thweasel/FujiSim_Test1/KiCad7/Z80Bus_Adapters/ZXspectrum_Concept/ZXspectrum_Concept.kicad_pcb

## KiCad design KiCad7/Z80Bus_Adapters/ZXspectrum_Concept/ZXspectrum_Concept.kicad_pcb (2023-06-03, an earlier design)

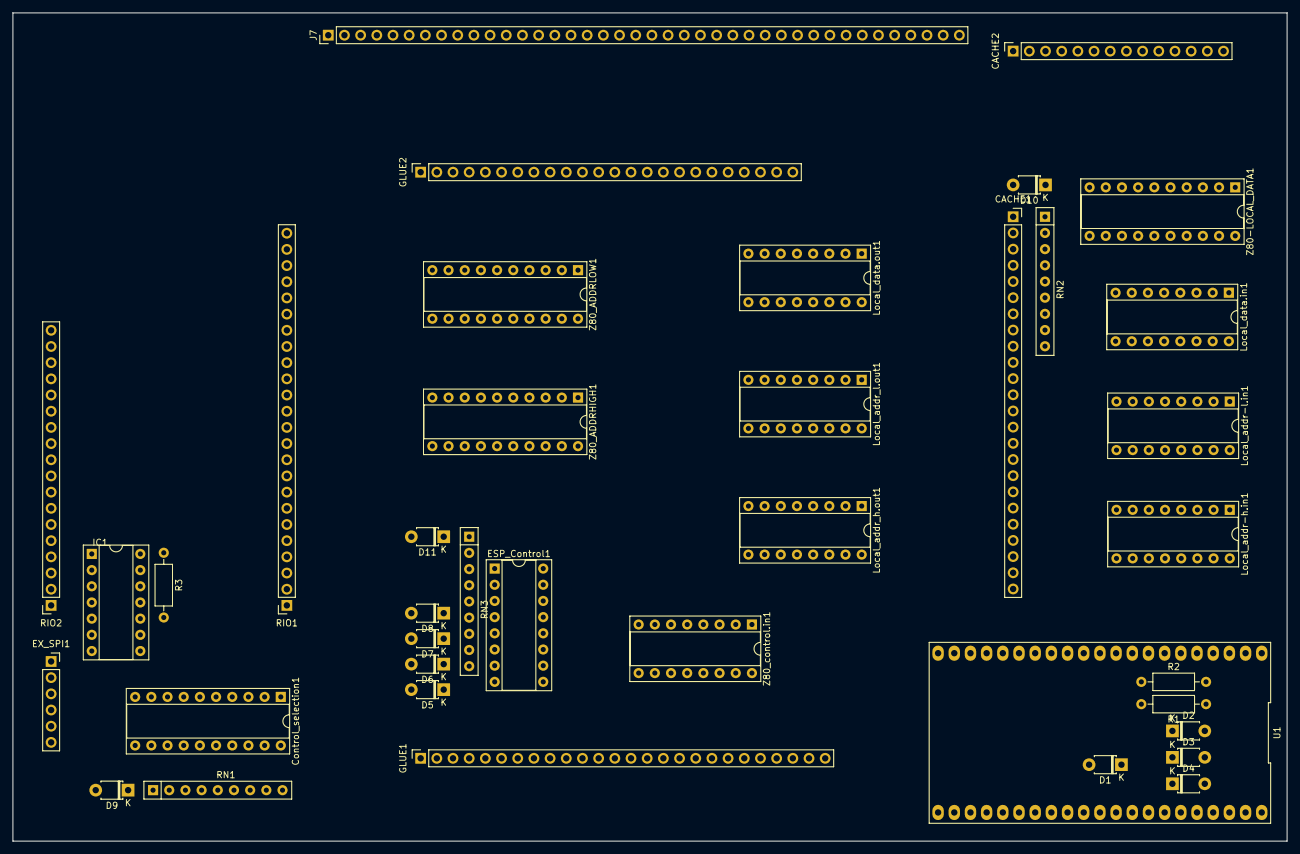
[picture p12: board ZXspectrum_Concept.kicad_pcb from above]

Board: 2 copper layers, 200.0 x 130.0 mm, 39 parts (0 on the bottom side), 130 nets, no tracks yet.

Parts:
CACHE1: Conn_01x24_Socket; PinSocket_1x24_P2.54mm_Vertical
CACHE2: Conn_01x14_Socket; PinSocket_1x14_P2.54mm_Vertical
Control_selection1: 74HC244N; DIP-20_W7.62mm_Socket
D1, D2, D3, D4, D5, D6, D7, D8, D9, D10, D11: 1N4148; D_T-1_P5.08mm_Horizontal
ESP_Control1: 74595N; DIP-16_W7.62mm_Socket
EX_SPI1: PinSocket_2.54mm; PinSocket_1x06_P2.54mm_Vertical
GLUE1: Conn_01x26_Socket; PinSocket_1x26_P2.54mm_Vertical
GLUE2: Conn_01x24_Socket; PinSocket_1x24_P2.54mm_Vertical
IC1: 74HC32N; DIP-14_W7.62mm_Socket
J7: DIAG-HOST_SYSTEM_BUS; PinHeader_1x40_P2.54mm_Vertical
Local_addr-h.in1: 74HC165N; DIP-16_W7.62mm_Socket
Local_addr-l.in1: 74HC165N; DIP-16_W7.62mm_Socket
Local_addr_h.out1: 74595N; DIP-16_W7.62mm_Socket
Local_addr_l.out1: 74595N; DIP-16_W7.62mm_Socket
Local_data.in1: 74HC165N; DIP-16_W7.62mm_Socket
Local_data.out1: 74595N; DIP-16_W7.62mm_Socket
R1, R2, R3: 22K; R_Axial_DIN0207_L6.3mm_D2.5mm_P10.16mm_Horizontal
RIO1: Conn_01x24_Socket; PinSocket_1x24_P2.54mm_Vertical
RIO2: Conn_01x18_Socket; PinSocket_1x18_P2.54mm_Vertical
RN1: LOCAL_CONTROL_BIAS; R_Array_SIP9
RN2, RN3: 4609M-101-103LF; R_Array_SIP9
U1: FREENOVE_ESP32-WROVER-DEV
Z80-LOCAL_DATA1, Z80_ADDRHIGH1, Z80_ADDRLOW1: 74HC245N; DIP-20_W7.62mm_Socket
Z80_control.in1: 74HC165N; DIP-16_W7.62mm_Socket

Connections:
+5V: CACHE2.1, Control_selection1.20 (VCC), D9.2 (A), D10.2 (A), D11.2 (A), ESP_Control1.16 (VCC), EX_SPI1.5, GLUE1.1, IC1.14 (VCC), Local_addr-h.in1.16 (VCC), Local_addr-l.in1.16 (VCC), Local_addr_h.out1.16 (VCC), Local_addr_l.out1.16 (VCC), Local_data.in1.16 (VCC), Local_data.out1.16 (VCC), R1.2, R3.1, RIO2.1, U1.20 (+5V), Z80-LOCAL_DATA1.20 (VCC), Z80_ADDRHIGH1.20 (VCC), Z80_ADDRLOW1.20 (VCC), Z80_control.in1.16 (VCC)
/CACHE connector/CACHE_CONTROL.A16: CACHE2.2, GLUE2.14
/CACHE connector/CACHE_CONTROL.CS: CACHE2.5, GLUE2.17
/CACHE connector/CACHE_CONTROL.DATASTATUS+PERM_Z80_IORQ: CACHE2.6, GLUE2.13
/CACHE connector/CACHE_CONTROL.OE: CACHE2.4, GLUE2.16
/CACHE connector/CACHE_CONTROL.WE: CACHE2.3, GLUE2.15
/CACHE connector/CACHE_DATASTATUS: CACHE2.12, GLUE2.5, RIO2.13
/CACHE connector/CACHE_SEL_0: CACHE2.8, RIO2.9
/CACHE connector/CACHE_SEL_1: CACHE2.9, RIO2.10
/CACHE connector/CACHE_SEL_2: CACHE2.10, RIO2.11
/CACHE connector/CACHE_SEL_3: CACHE2.11, RIO2.12
/CACHE connector/LOCAL_A0: CACHE1.9, Local_addr-l.in1.11 (D0), Local_addr_l.out1.15 (QA), Z80_ADDRLOW1.18 (B0)
/CACHE connector/LOCAL_A1: CACHE1.10, Local_addr-l.in1.12 (D1), Local_addr_l.out1.1 (QB), Z80_ADDRLOW1.17 (B1)
/CACHE connector/LOCAL_A2: CACHE1.11, Local_addr-l.in1.13 (D2), Local_addr_l.out1.2 (QC), Z80_ADDRLOW1.16 (B2)
/CACHE connector/LOCAL_A3: CACHE1.12, Local_addr-l.in1.14 (D3), Local_addr_l.out1.3 (QD), Z80_ADDRLOW1.15 (B3)
/CACHE connector/LOCAL_A4: CACHE1.13, Local_addr-l.in1.3 (D4), Local_addr_l.out1.4 (QE), Z80_ADDRLOW1.14 (B4)
/CACHE connector/LOCAL_A5: CACHE1.14, Local_addr-l.in1.4 (D5), Local_addr_l.out1.5 (QF), Z80_ADDRLOW1.13 (B5)
/CACHE connector/LOCAL_A6: CACHE1.15, Local_addr-l.in1.5 (D6), Local_addr_l.out1.6 (QG), Z80_ADDRLOW1.12 (B6)
/CACHE connector/LOCAL_A7: CACHE1.16, Local_addr-l.in1.6 (D7), Local_addr_l.out1.7 (QH), Z80_ADDRLOW1.11 (B7)
/CACHE connector/LOCAL_A8: CACHE1.17, Local_addr-h.in1.11 (D0), Local_addr_h.out1.15 (QA), Z80_ADDRHIGH1.18 (B0)
/CACHE connector/LOCAL_A9: CACHE1.18, Local_addr-h.in1.12 (D1), Local_addr_h.out1.1 (QB), Z80_ADDRHIGH1.17 (B1)
/CACHE connector/LOCAL_A10: CACHE1.19, Local_addr-h.in1.13 (D2), Local_addr_h.out1.2 (QC), Z80_ADDRHIGH1.16 (B2)
/CACHE connector/LOCAL_A11: CACHE1.20, Local_addr-h.in1.14 (D3), Local_addr_h.out1.3 (QD), Z80_ADDRHIGH1.15 (B3)
/CACHE connector/LOCAL_A12: CACHE1.21, Local_addr-h.in1.3 (D4), Local_addr_h.out1.4 (QE), Z80_ADDRHIGH1.14 (B4)
/CACHE connector/LOCAL_A13: CACHE1.22, Local_addr-h.in1.4 (D5), Local_addr_h.out1.5 (QF), Z80_ADDRHIGH1.13 (B5)
/CACHE connector/LOCAL_A14: CACHE1.23, Local_addr-h.in1.5 (D6), Local_addr_h.out1.6 (QG), Z80_ADDRHIGH1.12 (B6)
/CACHE connector/LOCAL_A15: CACHE1.24, Local_addr-h.in1.6 (D7), Local_addr_h.out1.7 (QH), Z80_ADDRHIGH1.11 (B7)
/CACHE connector/LOCAL_D0: CACHE1.1, Local_data.in1.11 (D0), Local_data.out1.15 (QA), RN2.2 (R1), Z80-LOCAL_DATA1.18 (B0)
/CACHE connector/LOCAL_D1: CACHE1.2, Local_data.in1.12 (D1), Local_data.out1.1 (QB), RN2.3 (R2), Z80-LOCAL_DATA1.17 (B1)
/CACHE connector/LOCAL_D2: CACHE1.3, Local_data.in1.13 (D2), Local_data.out1.2 (QC), RN2.4 (R3), Z80-LOCAL_DATA1.16 (B2)
/CACHE connector/LOCAL_D3: CACHE1.4, Local_data.in1.14 (D3), Local_data.out1.3 (QD), RN2.5 (R4), Z80-LOCAL_DATA1.15 (B3)
/CACHE connector/LOCAL_D4: CACHE1.5, Local_data.in1.3 (D4), Local_data.out1.4 (QE), RN2.6 (R5), Z80-LOCAL_DATA1.14 (B4)
/CACHE connector/LOCAL_D5: CACHE1.6, Local_data.in1.4 (D5), Local_data.out1.5 (QF), RN2.7 (R6), Z80-LOCAL_DATA1.13 (B5)
/CACHE connector/LOCAL_D6: CACHE1.7, Local_data.in1.5 (D6), Local_data.out1.6 (QG), RN2.8 (R7), Z80-LOCAL_DATA1.12 (B6)
/CACHE connector/LOCAL_D7: CACHE1.8, Local_data.in1.6 (D7), Local_data.out1.7 (QH), RN2.9 (R8), Z80-LOCAL_DATA1.11 (B7)
/CACHE connector/Z80_HARDLOCK: CACHE2.7, GLUE1.22, U1.4 (GPIO39)
/CORE/ESP_HARDLOCK: GLUE1.20, U1.26 (GPIO2)
/CORE/ESP_INT: D2.2 (A), D3.2 (A), D4.2 (A), R1.1, R2.2, U1.3 (GPIO36)
/CORE/ESP_PULSE: IC1.1, U1.11 (GPIO27)
/CORE/ESP_ROMSEL_0: GLUE1.18, U1.23 (GPIO7)
/CORE/ESP_ROMSEL_1: GLUE1.19, U1.22 (GPIO6)
/CORE/ESP_ROM_WR_PROTECT: GLUE1.17, U1.28 (GPIO4)
/CORE/ESP_SPI_INT.CE: Local_addr-h.in1.15 (~CE), Local_addr-l.in1.15 (~CE), Local_data.in1.15 (~CE), U1.31 (GPIO5), Z80_control.in1.15 (~CE)
/CORE/ESP_SPI_INT.MISO: Local_addr-h.in1.7 (~Q7), U1.33 (GPIO19)
/CORE/ESP_SPI_INT.MOSI: Local_data.out1.14 (SER), U1.39 (GPIO23)
/CORE/ESP_SPI_INT.MR: ESP_Control1.10 (~SRCLR), Local_addr_h.out1.10 (~SRCLR), Local_addr_l.out1.10 (~SRCLR), Local_data.out1.10 (~SRCLR), R3.2
/CORE/ESP_SPI_INT.OE: ESP_Control1.13 (~OE), Local_addr_h.out1.13 (~OE), Local_addr_l.out1.13 (~OE), U1.8 (GPIO33)
/CORE/ESP_SPI_INT.PL: Local_addr-h.in1.1 (~PL), Local_addr-l.in1.1 (~PL), Local_data.in1.1 (~PL), U1.9 (GPIO25), Z80_control.in1.1 (~PL)
/CORE/ESP_SPI_INT.SCK: ESP_Control1.11 (SRCLK), Local_addr-h.in1.2 (CP), Local_addr-l.in1.2 (CP), Local_addr_h.out1.11 (SRCLK), Local_addr_l.out1.11 (SRCLK), Local_data.in1.2 (CP), Local_data.out1.11 (SRCLK), U1.32 (GPIO18), Z80_control.in1.2 (CP)
/CORE/ESP_SPI_INT.STC: ESP_Control1.12 (RCLK), Local_addr_h.out1.12 (RCLK), Local_addr_l.out1.12 (RCLK), Local_data.out1.12 (RCLK), U1.10 (GPIO26)
/CORE/ESP_WAIT_RESET: GLUE2.6, U1.18 (GPIO11)
/CORE/EX_MISO: EX_SPI1.3, U1.13 (GPIO12)
/CORE/EX_MOSI: EX_SPI1.4, U1.15 (GPIO13)
/CORE/EX_SCK: EX_SPI1.2, U1.12 (GPIO14)
/CORE/EX_SS: EX_SPI1.1, U1.25 (GPIO8)
/CORE/SD_CARD_SS: U1.24 (GPIO15), U1.38 (GPIO22)
/CORE/Z80_HARDLOCK_RESET: D3.1 (K), GLUE2.3, RIO2.15
/GLUE connector/!ESP_HARDLOCK: Control_selection1.19 (2OE), GLUE1.21
/GLUE connector/PERM_Z80_IORQ: GLUE1.24, RIO2.17
/GLUE connector/RIO_CONTROL.A14: GLUE2.20, RIO2.4
/GLUE connector/RIO_CONTROL.A15: GLUE2.19, RIO2.3
/GLUE connector/RIO_CONTROL.A16: GLUE2.18, RIO2.2
/GLUE connector/RIO_CONTROL.CE: GLUE2.23, RIO2.6
/GLUE connector/RIO_CONTROL.OE: GLUE2.22, RIO2.7
/GLUE connector/RIO_CONTROL.ROM_RDY: GLUE2.24, RIO2.8
/GLUE connector/RIO_CONTROL.WE: GLUE2.21, RIO2.5
/GLUE connector/WAIT_IO: GLUE2.4, RIO2.14
/GLUE connector/Z80_BUS_CONTROL.Z80_ADD_DIR: GLUE2.10, Z80_ADDRHIGH1.1 (A->B), Z80_ADDRLOW1.1 (A->B)
/GLUE connector/Z80_BUS_CONTROL.Z80_ADD_OE: GLUE2.9, Z80_ADDRHIGH1.19 (CE), Z80_ADDRLOW1.19 (CE)
/GLUE connector/Z80_BUS_CONTROL.Z80_DATA_DIR: GLUE2.11, Z80-LOCAL_DATA1.1 (A->B)
/GLUE connector/Z80_BUS_CONTROL.Z80_DATA_OE: GLUE2.12, Z80-LOCAL_DATA1.19 (CE)
/GLUE connector/Z80_HARDLOCK_SET: GLUE2.2, RIO2.16
/RIO connector/Z80_A0: GLUE2.1, J7.18, RIO1.9, Z80_ADDRLOW1.2 (A0)
/RIO connector/Z80_A1: J7.17, RIO1.10, Z80_ADDRLOW1.3 (A1)
/RIO connector/Z80_A2: J7.16, RIO1.11, Z80_ADDRLOW1.4 (A2)
/RIO connector/Z80_A3: J7.15, RIO1.12, Z80_ADDRLOW1.5 (A3)
/RIO connector/Z80_A4: J7.14, RIO1.13, Z80_ADDRLOW1.6 (A4)
/RIO connector/Z80_A5: J7.13, RIO1.14, Z80_ADDRLOW1.7 (A5)
/RIO connector/Z80_A6: J7.12, RIO1.15, Z80_ADDRLOW1.8 (A6)
/RIO connector/Z80_A7: J7.11, RIO1.16, Z80_ADDRLOW1.9 (A7)
/RIO connector/Z80_A8: J7.26, RIO1.17, Z80_ADDRHIGH1.2 (A0)
/RIO connector/Z80_A9: J7.25, RIO1.18, Z80_ADDRHIGH1.3 (A1)
/RIO connector/Z80_A10: J7.24, RIO1.19, Z80_ADDRHIGH1.4 (A2)
/RIO connector/Z80_A11: J7.23, RIO1.20, Z80_ADDRHIGH1.5 (A3)
/RIO connector/Z80_A12: J7.22, RIO1.21, Z80_ADDRHIGH1.6 (A4)
/RIO connector/Z80_A13: J7.21, RIO1.22, Z80_ADDRHIGH1.7 (A5)
/RIO connector/Z80_A14: GLUE2.7, J7.20, RIO1.23, Z80_ADDRHIGH1.8 (A6)
/RIO connector/Z80_A15: GLUE2.8, J7.19, RIO1.24, Z80_ADDRHIGH1.9 (A7)
/RIO connector/Z80_D0: J7.34, RIO1.1, Z80-LOCAL_DATA1.2 (A0)
/RIO connector/Z80_D1: J7.33, RIO1.2, Z80-LOCAL_DATA1.3 (A1)
/RIO connector/Z80_D2: J7.32, RIO1.3, Z80-LOCAL_DATA1.4 (A2)
/RIO connector/Z80_D3: J7.31, RIO1.4, Z80-LOCAL_DATA1.5 (A3)
/RIO connector/Z80_D4: J7.30, RIO1.5, Z80-LOCAL_DATA1.6 (A4)
/RIO connector/Z80_D5: J7.29, RIO1.6, Z80-LOCAL_DATA1.7 (A5)
/RIO connector/Z80_D6: J7.28, RIO1.7, Z80-LOCAL_DATA1.8 (A6)
/RIO connector/Z80_D7: J7.27, RIO1.8, Z80-LOCAL_DATA1.9 (A7)
/SPI/ESP_CONTROL.BUSRQ: Control_selection1.1 (1OE), D8.1 (K), ESP_Control1.4 (QE), GLUE1.15, RN3.6 (R5)
/SPI/ESP_CONTROL.IORQ: Control_selection1.6 (1A2), Control_selection1.13 (2A2), ESP_Control1.2 (QC), GLUE1.13, RN3.4 (R3)
/SPI/ESP_CONTROL.MEMRQ: Control_selection1.8 (1A3), Control_selection1.11 (2A3), ESP_Control1.3 (QD), GLUE1.14, RN3.5 (R4)
/SPI/ESP_CONTROL.NMI: D5.1 (K), ESP_Control1.7 (QH), RN3.9 (R8)
/SPI/ESP_CONTROL.RD: Control_selection1.2 (1A0), Control_selection1.17 (2A0), ESP_Control1.15 (QA), RN3.2 (R1)
/SPI/ESP_CONTROL.ROMCS: D6.1 (K), ESP_Control1.6 (QG), GLUE1.16, RN3.8 (R7)
/SPI/ESP_CONTROL.WAIT: D7.1 (K), ESP_Control1.5 (QF), RN3.7 (R6)
/SPI/ESP_CONTROL.WR: ESP_Control1.1 (QB), GLUE1.12, IC1.2, Local_data.out1.13 (~OE), RN3.3 (R2)
/SPI/ESP_CONTROL.WR+ESP_PULSE: Control_selection1.4 (1A1), Control_selection1.15 (2A1), IC1.3
/SPI/LOCAL_CONTROL.IORQ: Control_selection1.14 (1Y2), GLUE1.10, RN1.3 (R2)
/SPI/LOCAL_CONTROL.MEMRQ: Control_selection1.12 (1Y3), GLUE1.11, RN1.2 (R1)
/SPI/LOCAL_CONTROL.RD: Control_selection1.18 (1Y0), GLUE1.8, RN1.5 (R4)
/SPI/LOCAL_CONTROL.WR: Control_selection1.16 (1Y1), GLUE1.9, RN1.4 (R3)
/SPI/Z80_CONTROL.BUSACK: D4.1 (K), J7.9, Z80_control.in1.5 (D6)
/SPI/Z80_CONTROL.BUSRQ: D8.2 (A), GLUE1.6, J7.5, Z80_control.in1.3 (D4)
/SPI/Z80_CONTROL.IORQ: Control_selection1.7 (2Y2), GLUE1.4, J7.3, Z80_control.in1.13 (D2)
/SPI/Z80_CONTROL.MEMRQ: Control_selection1.9 (2Y3), GLUE1.5, J7.4, Z80_control.in1.14 (D3)
/SPI/Z80_CONTROL.NMI: D5.2 (A), J7.7, Z80_control.in1.6 (D7)
/SPI/Z80_CONTROL.RD: Control_selection1.3 (2Y0), GLUE1.2, J7.1, Z80_control.in1.11 (D0)
/SPI/Z80_CONTROL.RESET: D1.2 (A), J7.10
/SPI/Z80_CONTROL.ROMCS: D6.2 (A), J7.8
/SPI/Z80_CONTROL.WAIT: D2.1 (K), D7.2 (A), GLUE1.7, J7.6, Z80_control.in1.4 (D5)
/SPI/Z80_CONTROL.WR: Control_selection1.5 (2Y1), GLUE1.3, J7.2, Z80_control.in1.12 (D1)
GND: CACHE2.14, Control_selection1.10 (GND), ESP_Control1.8 (GND), EX_SPI1.6, GLUE1.26, IC1.4, IC1.5, IC1.7 (GND), IC1.9, IC1.10, IC1.12, IC1.13, J7.40, Local_addr-h.in1.8 (GND), Local_addr-l.in1.8 (GND), Local_addr_h.out1.8 (GND), Local_addr_l.out1.8 (GND), Local_data.in1.8 (GND), Local_data.in1.10 (DS), Local_data.out1.8 (GND), R2.1, RIO2.18, U1.21 (GND), U1.34 (GND), U1.40 (GND), Z80-LOCAL_DATA1.10 (GND), Z80_ADDRHIGH1.10 (GND), Z80_ADDRLOW1.10 (GND), Z80_control.in1.8 (GND)
unnamed: D1.1 (K), U1.35 (GPIO21)
unnamed: D9.1 (K), RN1.1 (common)
unnamed: D10.1 (K), RN2.1 (common)
unnamed: D11.1 (K), RN3.1 (common)
unnamed: ESP_Control1.9 (QH'), Local_addr_l.out1.14 (SER)
unnamed: ESP_Control1.14 (SER), Local_data.out1.9 (QH')
unnamed: Local_addr-h.in1.10 (DS), Local_addr-l.in1.7 (~Q7)
unnamed: Local_addr-l.in1.10 (DS), Z80_control.in1.7 (~Q7)
unnamed: Local_addr_h.out1.14 (SER), Local_addr_l.out1.9 (QH')
unnamed: Local_data.in1.7 (~Q7), Z80_control.in1.10 (DS)
