thweasel/FujiSim_Test1/KiCad7/Z80Bus_ReferenceDesign/FujiNet_FinishedPCBs/FujiNet_Z80Bus_Reference_singleboard.kicad_pcb

## KiCad design KiCad7/Z80Bus_ReferenceDesign/FujiNet_FinishedPCBs/FujiNet_Z80Bus_Reference_singleboard.kicad_pcb (2023-05-09)

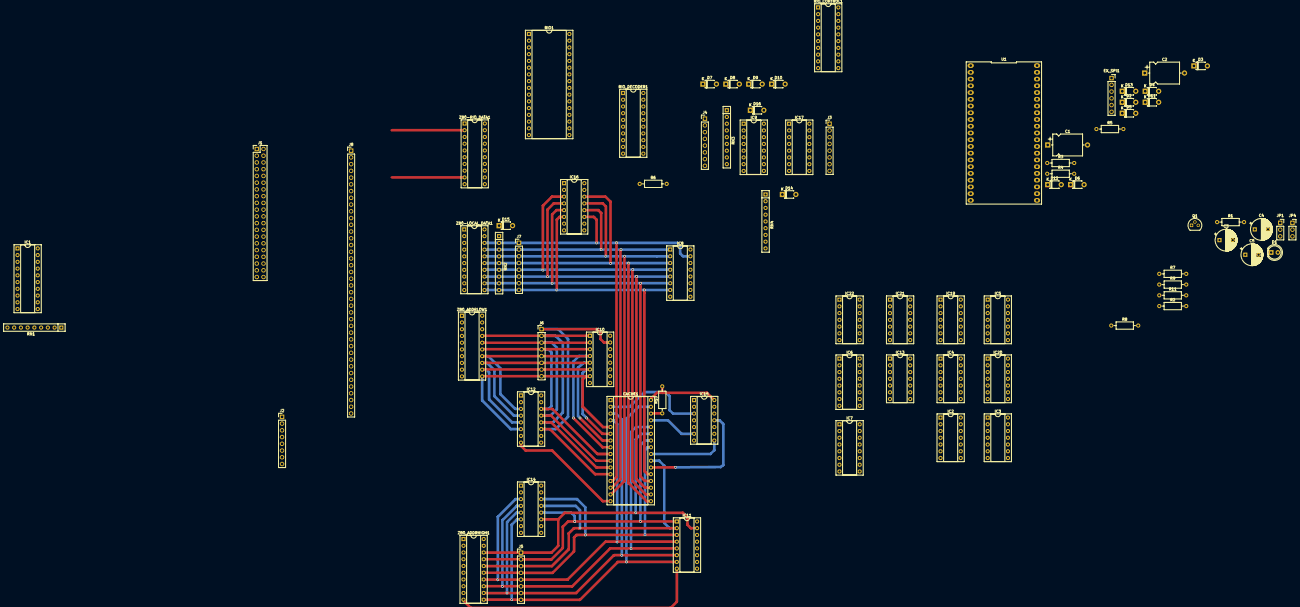
[picture p13: board FujiNet_Z80Bus_Reference_singleboard.kicad_pcb from above]

Board: 2 copper layers, 78 parts (0 on the bottom side), 165 nets.

Parts:
C1, C2: 10UF; CP_Axial_L11.0mm_D8.0mm_P15.00mm_Horizontal
C3: 10 uf; CP_Radial_D8.0mm_P5.00mm
C4, C5: .1 uf; CP_Radial_D8.0mm_P5.00mm
CACHE1: AS6C1008-55PCN; DIP-32_W15.24mm_Socket
D1: POWER_LED; LED_D5.0mm
D2, D3, D4, D5, D6, D7, D8, D9, D10, D11, D12, D13, D14, D15, D16: 1N4148; D_T-1_P5.08mm_Horizontal
EX_SPI1: PINHD-1X6; PinSocket_1x06_P2.54mm_Vertical
IC1: 74244N; DIP-20_W7.62mm_Socket
IC2: 7404N; DIP-14_W7.62mm_Socket
IC3: 7474N; DIP-14_W7.62mm_Socket
IC4, IC13, IC19, IC21, IC22: 7432N; DIP-14_W7.62mm_Socket
IC5, IC15, IC20: 7408N; DIP-14_W7.62mm_Socket
IC6, IC7: 74590N; DIP-16_W7.62mm_Socket
IC8, IC9, IC10, IC11: 74595N; DIP-16_W7.62mm_Socket
IC12, IC14, IC16, IC17: 74165N; DIP-16_W7.62mm_Socket
J1: HOST SYSTEM HEADER; PinHeader_2x20_P2.54mm_Vertical
J2: DIAG-ESP_SPI; PinHeader_1x08_P2.54mm_Vertical
J3: DIAG-Z80_CONTROL; PinHeader_1x08_P2.54mm_Vertical
J4: DIAG-ESP_CONTROL; PinHeader_1x08_P2.54mm_Vertical
J5: DIAG-LOCAL_ADD_HIGH; PinHeader_1x08_P2.54mm_Vertical
J6: DIAG-LOCAL_ADD_LOW; PinHeader_1x08_P2.54mm_Vertical
J7: DIAG-LOCAL_DATA; PinHeader_1x08_P2.54mm_Vertical
J8: DIAG-HOST_SYSTEM_BUS; PinHeader_1x40_P2.54mm_Vertical
JP1: PINHD-ADDR_FILTER; PinSocket_1x03_P2.54mm_Vertical
JP4: PINHD-POWER/RESET; PinSocket_1x03_P2.54mm_Vertical
Q1: 2N2222 (BC337); TO-92
R1, R2, R7: 1K; R_Axial_DIN0207_L6.3mm_D2.5mm_P10.16mm_Horizontal
R3, R4, R5, R6: 22K; R_Axial_DIN0207_L6.3mm_D2.5mm_P10.16mm_Horizontal
R8, R9, R10, R11: 10K; R_Axial_DIN0207_L6.3mm_D2.5mm_P10.16mm_Horizontal
RIO1: AS6C1008-55PCN; DIP-32_W15.24mm_Socket
RIO_CONTROL1: 74244N; DIP-20_W7.62mm_Socket
RIO_DECODER1: 74245N; DIP-20_W7.62mm_Socket
RN1, RN2, RN3, RN4: 4609M-101-103LF; R_Array_SIP9
U1: FREENOVE_ESP32-WROVER-DEV
Z80-LOCAL_DATA1, Z80-RIO_DATA1, Z80_ADDRHIGH1, Z80_ADDRLOW1: 74245N; DIP-20_W7.62mm_Socket

Connections:
/!CACHE_DATASTATUS: IC21.2, Q1.1, R7.1
/CACHE/CACHE_CE2: CACHE1.30, R10.1
/CACHE/CACHE_CS: CACHE1.22, IC15.11
/CACHE/CACHE_DATASTATUS+PERM_Z80_IORQ: IC6.11, IC6.13, IC13.6
/CACHE/CACHE_OE: CACHE1.24, IC15.8
/CACHE/CACHE_WE: CACHE1.29, IC15.6
/CACHE/LOCAL_ADD_0: CACHE1.12, IC6.15, IC10.15, IC12.11, J6.1, Z80_ADDRLOW1.18
/CACHE/LOCAL_ADD_1: CACHE1.11, IC6.1, IC10.1, IC12.12, J6.2, Z80_ADDRLOW1.17
/CACHE/LOCAL_ADD_2: CACHE1.10, IC6.2, IC10.2, IC12.13, J6.3, Z80_ADDRLOW1.16
/CACHE/LOCAL_ADD_3: CACHE1.9, IC6.3, IC10.3, IC12.14, J6.4, Z80_ADDRLOW1.15
/CACHE/LOCAL_ADD_4: CACHE1.8, IC6.4, IC10.4, IC12.3, J6.5, Z80_ADDRLOW1.14
/CACHE/LOCAL_ADD_5: CACHE1.7, IC6.5, IC10.5, IC12.4, J6.6, Z80_ADDRLOW1.13
/CACHE/LOCAL_ADD_6: CACHE1.6, IC6.6, IC10.6, IC12.5, J6.7, Z80_ADDRLOW1.12
/CACHE/LOCAL_ADD_7: CACHE1.5, IC6.7, IC10.7, IC12.6, J6.8, Z80_ADDRLOW1.11
/CACHE/LOCAL_ADD_8: CACHE1.27, IC7.15, IC11.15, IC14.11, J5.1, Z80_ADDRHIGH1.18
/CACHE/LOCAL_ADD_9: CACHE1.26, IC7.1, IC11.1, IC14.12, J5.2, Z80_ADDRHIGH1.17
/CACHE/LOCAL_ADD_10: CACHE1.23, IC7.2, IC11.2, IC14.13, J5.3, Z80_ADDRHIGH1.16
/CACHE/LOCAL_ADD_11: CACHE1.25, IC7.3, IC11.3, IC14.14, J5.4, Z80_ADDRHIGH1.15
/CACHE/LOCAL_ADD_12: CACHE1.4, IC11.4, IC14.3, J5.5, Z80_ADDRHIGH1.14
/CACHE/LOCAL_DATA_0: CACHE1.13, IC8.15, IC16.11, J7.1, RN2.2, Z80-LOCAL_DATA1.18
/CACHE/LOCAL_DATA_1: CACHE1.14, IC8.1, IC16.12, J7.2, RN2.3, Z80-LOCAL_DATA1.17
/CACHE/LOCAL_DATA_2: CACHE1.15, IC8.2, IC16.13, J7.3, RN2.4, Z80-LOCAL_DATA1.16
/CACHE/LOCAL_DATA_3: CACHE1.17, IC8.3, IC16.14, J7.4, RN2.5, Z80-LOCAL_DATA1.15
/CACHE/LOCAL_DATA_4: CACHE1.18, IC8.4, IC16.3, J7.5, RN2.6, Z80-LOCAL_DATA1.14
/CACHE/LOCAL_DATA_5: CACHE1.19, IC8.5, IC16.4, J7.6, RN2.7, Z80-LOCAL_DATA1.13
/CACHE/LOCAL_DATA_6: CACHE1.20, IC8.6, IC16.5, J7.7, RN2.8, Z80-LOCAL_DATA1.12
/CACHE/LOCAL_DATA_7: CACHE1.21, IC8.7, IC16.6, J7.8, RN2.9, Z80-LOCAL_DATA1.11
/CACHE_DATASTATUS: IC6.12, IC6.14, IC7.12, IC7.14, IC13.5, IC15.1, R2.1, R9.1, RIO_DECODER1.14
/CACHE_SEL_0: CACHE1.28, IC11.5, IC14.4, J5.6, RIO_DECODER1.18, Z80_ADDRHIGH1.13
/CACHE_SEL_1: CACHE1.3, IC11.6, IC14.5, J5.7, RIO_DECODER1.17, Z80_ADDRHIGH1.12
/CACHE_SEL_2: CACHE1.31, IC11.7, IC14.6, J5.8, RIO_DECODER1.16, Z80_ADDRHIGH1.11
/CACHE_SEL_3: CACHE1.2, IC15.3, RIO_DECODER1.15
/CORE/!ESP_HARDLOCK: IC1.1, IC2.2
/CORE/CLR_Z80_HARDLOCK: IC3.1, IC5.3
/CORE/ESP_CONTROL_Z80: D2.1, D3.1, IC1.19
/CORE/ESP_HARDLOCK: IC2.1, IC13.2, IC13.9, U1.26
/CORE/ESP_INT: D6.2, D11.2, D12.2, R3.2, R5.2, U1.3
/CORE/ESP_PULSE: IC13.12, U1.11
/CORE/ESP_SPI.CE: IC12.15, IC14.15, IC16.15, IC17.15, J2.7, U1.31
/CORE/ESP_SPI.MISO: IC14.9, J2.2, U1.33
/CORE/ESP_SPI.MOSI: IC8.14, J2.1, U1.39
/CORE/ESP_SPI.OE: IC9.13, IC10.13, IC11.13, J2.5, U1.8
/CORE/ESP_SPI.PL: IC12.1, IC14.1, IC16.1, IC17.1, J2.8, U1.9
/CORE/ESP_SPI.SCK: IC8.11, IC9.11, IC10.11, IC11.11, IC12.2, IC14.2, IC16.2, IC17.2, J2.6, U1.32
/CORE/ESP_SPI.STC: IC8.12, IC9.12, IC10.12, IC11.12, J2.3, U1.10
/CORE/ESP_WAIT_RESET: C1.1, IC3.13, RN1.8, U1.18
/CORE/EX_MISO: EX_SPI1.3, U1.13
/CORE/EX_MOSI: EX_SPI1.4, U1.15
/CORE/EX_SCK: EX_SPI1.2, U1.12
/CORE/EX_SS: EX_SPI1.1, U1.25
/CORE/IORQ_FILTER_BIT: IC21.12, JP1.2
/CORE/PRE_Z80_HARDLOCK: IC3.4, IC13.3
/CORE/SD_CARD_SS: U1.24, U1.38
/CORE/SPIBUS/ESP_SPI.MR: IC8.10, IC9.10, IC10.10, IC11.10, R6.2
/CORE/Z80_ADD_CONNECT: D2.2, IC22.1, RN1.6
/CORE/Z80_DATA_CONNECT: D3.2, IC21.10, IC22.12, RN1.7
/ESP_CONTROL_BUSRQ: D7.1, IC4.10, IC9.4, J4.5, RN3.6
/ESP_CONTROL_IORQ: IC1.8, IC1.17, IC5.5, IC9.3, J4.4, RN3.4
/ESP_CONTROL_MEMRQ: IC1.6, IC1.15, IC5.4, IC9.2, IC22.5, J4.3, RN3.5
/ESP_CONTROL_NMI: D10.1, IC9.7, J4.8, RN3.9
/ESP_CONTROL_RD: IC1.2, IC1.11, IC9.15, J4.1, RN3.2
/ESP_CONTROL_ROMCS: D9.1, IC9.6, IC19.9, J4.7, RN3.8
/ESP_CONTROL_WAIT: D8.1, IC9.5, J4.6, RN3.7
/ESP_CONTROL_WR: IC8.13, IC9.1, IC13.13, IC21.9, J2.4, J4.2, RN3.3
/ESP_IOD_CONFIG: IC4.8, IC19.1, IC19.5, IC20.5, IC20.12, IC22.4
/ESP_ROMSEL_0: RIO_CONTROL1.11, U1.23
/ESP_ROMSEL_1: RIO_CONTROL1.13, U1.22
/LOCAL_IORQ: IC1.14, IC15.2, RN1.5
/LOCAL_MEMRQ: IC1.12, IC15.13, RN1.4
/LOCAL_RD: IC1.18, IC15.10, RN1.2
/LOCAL_WR: IC1.16, IC15.5, RN1.3
/PERM_Z80_IORQ: IC13.4, IC15.12, IC20.1, IC20.4, IC21.1, IC21.5, IC21.11, IC22.13, RIO_DECODER1.19
/RIO/DEC14: RIO1.3, RIO_CONTROL1.9, RIO_CONTROL1.18, RN4.2
/RIO/DEC15: RIO1.31, RIO_CONTROL1.7, RIO_CONTROL1.16, RN4.3
/RIO/DEC16: IC20.6, IC20.10, RIO1.2, RIO_CONTROL1.1
/RIO/DEC_CE: IC20.8, RIO1.22
/RIO/DEC_OE: RIO1.24, RIO_CONTROL1.3, RIO_CONTROL1.12, RN4.5, Z80-RIO_DATA1.1
/RIO/DEC_WE: RIO1.29, RIO_CONTROL1.5, RIO_CONTROL1.14, RN4.4
/RIO/ESP_IOD_CONFIG+Z80_WR: IC19.3, RIO_CONTROL1.6
/RIO/RIO_CE2: R11.1, RIO1.30
/RIO/ROM_D0: RIO1.13, RIO_DECODER1.2, Z80-RIO_DATA1.18
/RIO/ROM_D1: RIO1.14, RIO_DECODER1.3, Z80-RIO_DATA1.17
/RIO/ROM_D2: RIO1.15, RIO_DECODER1.4, Z80-RIO_DATA1.16
/RIO/ROM_D3: RIO1.17, RIO_DECODER1.5, Z80-RIO_DATA1.15
/RIO/ROM_D4: RIO1.18, RIO_DECODER1.6, Z80-RIO_DATA1.14
/RIO/ROM_D5: RIO1.19, RIO_DECODER1.7, Z80-RIO_DATA1.13
/RIO/ROM_D6: RIO1.20, RIO_DECODER1.8, Z80-RIO_DATA1.12
/RIO/ROM_D7: RIO1.21, RIO_DECODER1.9, Z80-RIO_DATA1.11
/RIO/ROM_D_RDY: IC19.8, IC20.13, RIO_CONTROL1.19, Z80-RIO_DATA1.19
/RIO/ROM_WR_PROTECT+Z80_WR: IC19.11, RIO_CONTROL1.15
/RIO/Z80_A0: J1.1, J8.20, RIO1.12, Z80_ADDRLOW1.2
/RIO/Z80_A1: J1.2, J8.21, RIO1.11, Z80_ADDRLOW1.3
/RIO/Z80_A2: J1.3, J8.22, RIO1.10, Z80_ADDRLOW1.4
/RIO/Z80_A3: J1.4, J8.23, RIO1.9, Z80_ADDRLOW1.5
/RIO/Z80_A4: J1.5, J8.24, RIO1.8, Z80_ADDRLOW1.6
/RIO/Z80_A5: J1.6, J8.25, RIO1.7, Z80_ADDRLOW1.7
/RIO/Z80_A6: J1.7, J8.26, RIO1.6, Z80_ADDRLOW1.8
/RIO/Z80_A7: J1.8, J8.27, RIO1.5, Z80_ADDRLOW1.9
/RIO/Z80_A8: J1.33, J8.28, RIO1.27, Z80_ADDRHIGH1.2
/RIO/Z80_A9: J1.34, J8.29, RIO1.26, Z80_ADDRHIGH1.3
/RIO/Z80_A10: J1.35, J8.30, RIO1.23, Z80_ADDRHIGH1.4
/RIO/Z80_A11: J1.36, J8.31, RIO1.25, Z80_ADDRHIGH1.5
/RIO/Z80_A12: J1.37, J8.32, RIO1.4, Z80_ADDRHIGH1.6
/RIO/Z80_A13: J1.38, J8.33, RIO1.28, Z80_ADDRHIGH1.7
/RIO/Z80_A14: J1.39, J8.34, RIO_CONTROL1.2, Z80_ADDRHIGH1.8
/RIO/Z80_A15: J1.40, J8.35, RIO_CONTROL1.4, Z80_ADDRHIGH1.9
/RIO/Z80_D0: J1.9, J8.12, Z80-LOCAL_DATA1.2, Z80-RIO_DATA1.2
/RIO/Z80_D1: J1.10, J8.13, Z80-LOCAL_DATA1.3, Z80-RIO_DATA1.3
/RIO/Z80_D2: J1.11, J8.14, Z80-LOCAL_DATA1.4, Z80-RIO_DATA1.4
/RIO/Z80_D3: J1.12, J8.15, Z80-LOCAL_DATA1.5, Z80-RIO_DATA1.5
/RIO/Z80_D4: J1.13, J8.16, Z80-LOCAL_DATA1.6, Z80-RIO_DATA1.6
/RIO/Z80_D5: J1.14, J8.17, Z80-LOCAL_DATA1.7, Z80-RIO_DATA1.7
/RIO/Z80_D6: J1.15, J8.18, Z80-LOCAL_DATA1.8, Z80-RIO_DATA1.8
/RIO/Z80_D7: J1.16, J8.19, Z80-LOCAL_DATA1.9, Z80-RIO_DATA1.9
/RIO/Z80_RD+ESP_IOD_CONFIG+PERM_Z80_IORQ: IC20.3, RIO_CONTROL1.8
/ROM_WR_PROTECT: IC19.13, U1.28
/WAIT_IO: IC2.9, RIO_DECODER1.13
/Z80 BUS/Z80_ADD_DIR: IC22.6, Z80_ADDRHIGH1.1, Z80_ADDRLOW1.1
/Z80 BUS/Z80_ADD_OE: IC22.3, Z80_ADDRHIGH1.19, Z80_ADDRLOW1.19
/Z80 BUS/Z80_DATA_DIR: IC22.8, Z80-LOCAL_DATA1.1
/Z80 BUS/Z80_DATA_OE: IC22.11, Z80-LOCAL_DATA1.19
/Z80_BUSACK: IC17.6, J1.24, J3.8, J8.10
/Z80_BUSRQ: D7.2, IC17.3, J1.28, J3.5, J8.6
/Z80_HARDLOCK: IC3.5, IC6.10, IC7.10, U1.4
/Z80_HARDLOCK_RESET: D11.1, IC2.5, RIO_DECODER1.12
/Z80_HARDLOCK_SET: IC2.3, RIO_DECODER1.11
/Z80_IORQ: IC1.5, IC13.10, IC17.13, J1.29, J3.3, J8.5
/Z80_MEMRQ: IC1.3, IC17.14, IC19.10, J1.30, J3.4, J8.4
/Z80_NMI: D10.2, D12.1, IC17.5, J1.26, J3.7, J8.8
/Z80_RD: IC1.9, IC15.9, IC17.11, IC19.4, IC21.4, J1.32, J3.1, J8.2, RIO_CONTROL1.17
/Z80_RESET: D4.2, J1.23, J8.11, JP4.1
/Z80_ROMCS: D9.2, J1.25, J8.9
/Z80_WAIT: D6.1, D8.2, D13.2, IC17.4, J1.27, J3.6, J8.7
/Z80_WR: IC1.7, IC15.4, IC17.12, IC19.2, IC19.12, J1.31, J3.2, J8.3
GND: C1.2, C2.2, C3.2, C4.2, C5.2, CACHE1.16, D1.2, EX_SPI1.6, IC16.10, J1.21, J8.1, JP1.1, JP4.2, Q1.3, R5.1, RIO1.16, U1.14, U1.21, U1.34, U1.40
unnamed: C2.1, IC5.1, R4.2
unnamed: D1.1, R1.1
unnamed: D4.1, U1.35
unnamed: D5.1, RN1.1
unnamed: D13.1, IC3.8
unnamed: D14.1, RN4.1
unnamed: D15.1, RN2.1
unnamed: D16.1, RN3.1
unnamed: IC1.4, IC1.13, IC13.11
unnamed: IC2.6, IC5.2
unnamed: IC2.8, IC3.10
unnamed: IC2.10, IC4.9
unnamed: IC2.11, IC5.6
unnamed: IC6.9, IC7.11, IC7.13
unnamed: IC8.9, IC9.14
unnamed: IC10.9, IC11.14
unnamed: IC9.9, IC10.14
unnamed: IC12.9, IC14.10
unnamed: IC12.10, IC17.9
unnamed: IC2.4, IC13.1
unnamed: IC13.8, IC21.13
unnamed: IC16.9, IC17.10
unnamed: IC19.6, IC20.2
unnamed: IC20.9, IC20.11
unnamed: IC21.3, IC22.2
unnamed: IC21.6, IC22.9
unnamed: IC21.8, IC22.10
unnamed: Q1.2, R2.2
unnamed: R8.1, RIO_DECODER1.1
VCC: C3.1, C4.1, C5.1, CACHE1.32, D5.2, D14.2, D15.2, D16.2, EX_SPI1.5, J1.22, JP4.3, R1.2, R3.1, R4.1, R6.1, R7.2, R8.2, R9.2, R10.2, R11.2, RIO1.32, U1.19, U1.20
