thweasel/FujiSim_Test1/KiCad7/FujiNet_Z80Bus_Modules/RIO-128K_ZXspectrum/RIO-128K_ZXspectrum_connector.kicad_sch

## KiCad design KiCad7/FujiNet_Z80Bus_Modules/RIO-128K_ZXspectrum/RIO-128K_ZXspectrum_connector.kicad_sch (2023-06-01)

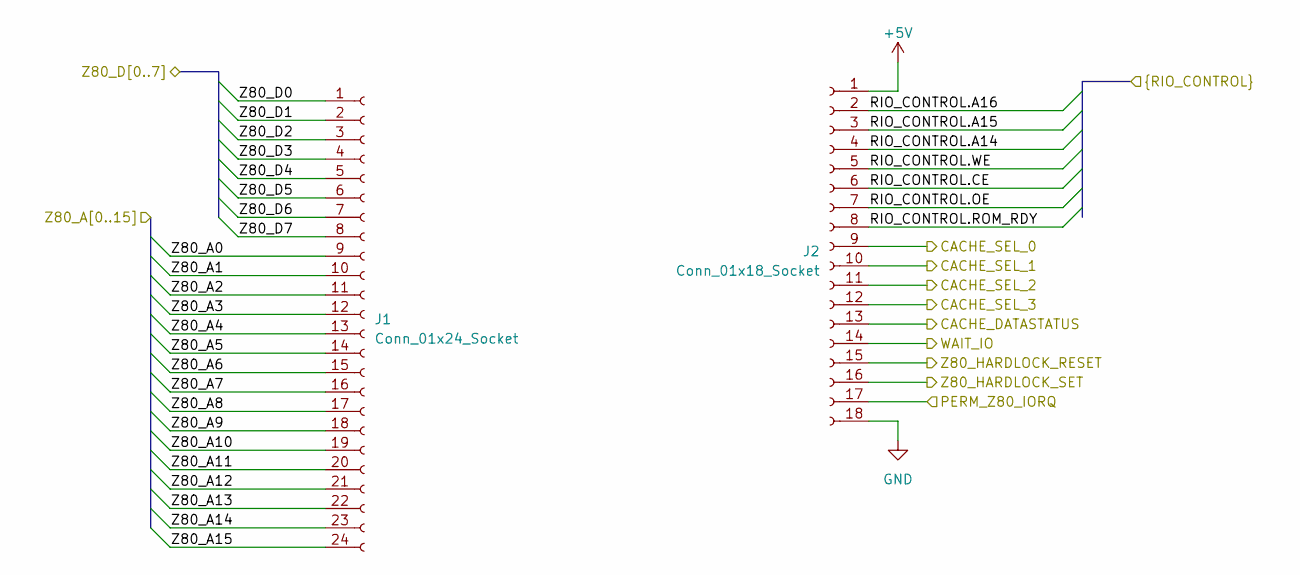
[picture p14: schematic RIO-128K_ZXspectrum_connector.kicad_sch]

Parts:
J1: Conn_01x24_Socket; PinSocket_1x24_P2.54mm_Vertical
J2: Conn_01x18_Socket; PinSocket_1x18_P2.54mm_Vertical

Connections:
+5V: J2.1
CACHE_DATASTATUS: J2.13
CACHE_SEL_0: J2.9
CACHE_SEL_1: J2.10
CACHE_SEL_2: J2.11
CACHE_SEL_3: J2.12
GND: J2.18
PERM_Z80_IORQ: J2.17
RIO_CONTROL.A14: J2.4
RIO_CONTROL.A15: J2.3
RIO_CONTROL.A16: J2.2
RIO_CONTROL.CE: J2.6
RIO_CONTROL.OE: J2.7
RIO_CONTROL.ROM_RDY: J2.8
RIO_CONTROL.WE: J2.5
WAIT_IO: J2.14
Z80_A0: J1.9
Z80_A1: J1.10
Z80_A2: J1.11
Z80_A3: J1.12
Z80_A4: J1.13
Z80_A5: J1.14
Z80_A6: J1.15
Z80_A7: J1.16
Z80_A8: J1.17
Z80_A9: J1.18
Z80_A10: J1.19
Z80_A11: J1.20
Z80_A12: J1.21
Z80_A13: J1.22
Z80_A14: J1.23
Z80_A15: J1.24
Z80_D0: J1.1
Z80_D1: J1.2
Z80_D2: J1.3
Z80_D3: J1.4
Z80_D4: J1.5
Z80_D5: J1.6
Z80_D6: J1.7
Z80_D7: J1.8
Z80_HARDLOCK_RESET: J2.15
Z80_HARDLOCK_SET: J2.16
