thweasel/FujiSim_Test1/KiCad7/FujiNet_Z80Bus_Modules/SPI-Z80-BUS_ZXspectrum/SPI-Z080-BUS_read.kicad_sch

## KiCad design KiCad7/FujiNet_Z80Bus_Modules/SPI-Z80-BUS_ZXspectrum/SPI-Z080-BUS_read.kicad_sch (2023-06-03)

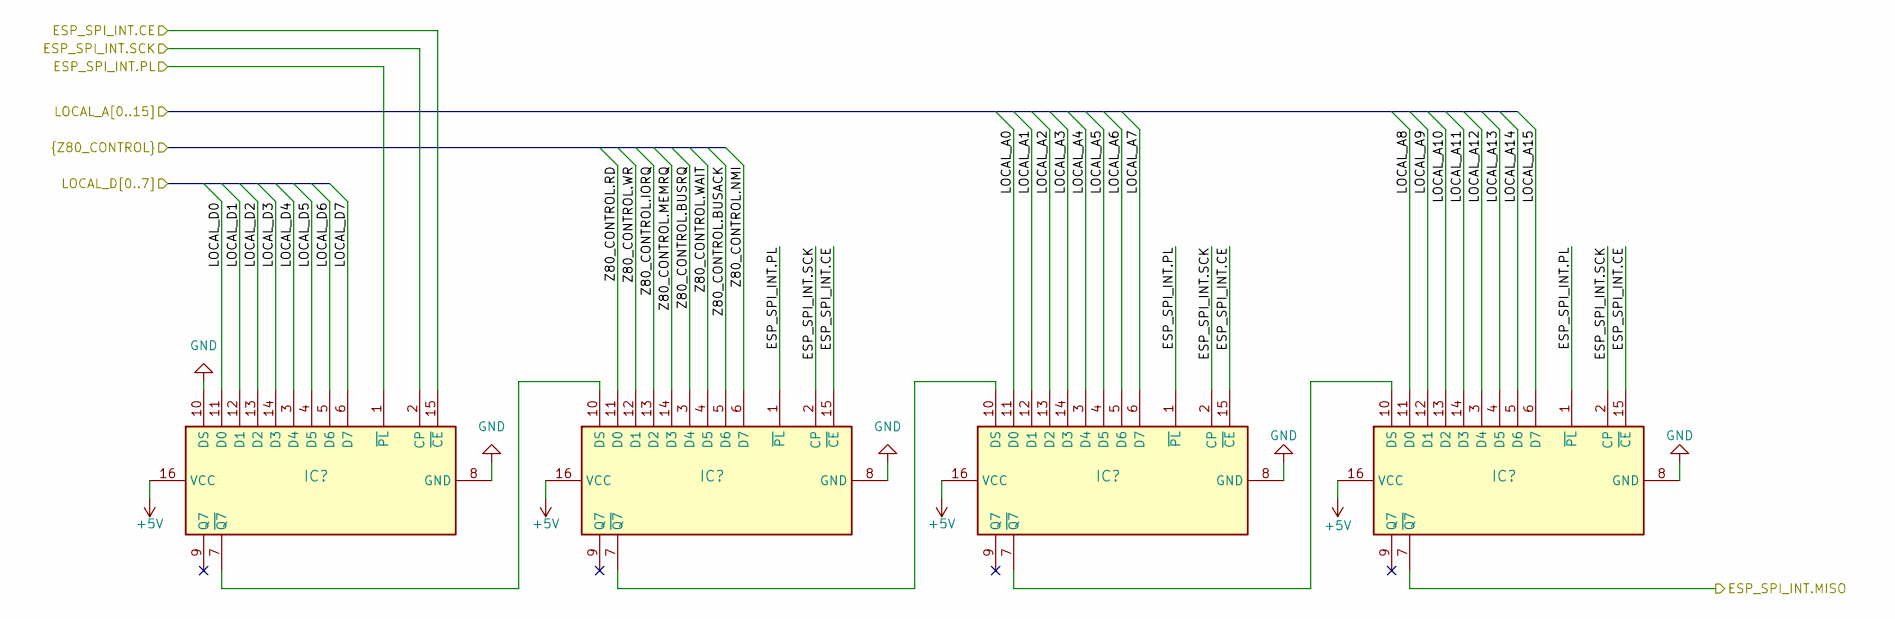
[picture p15: schematic SPI-Z080-BUS_read.kicad_sch]

Parts:
IC1, IC2, IC3, IC4: 74HC165N; DIP-16_W7.62mm_Socket

Connections:
+5V: IC1.16 (VCC), IC2.16 (VCC), IC3.16 (VCC), IC4.16 (VCC)
ESP_SPI_INT.CE: IC1.15 (~CE), IC2.15 (~CE), IC3.15 (~CE), IC4.15 (~CE)
ESP_SPI_INT.MISO: IC4.7 (~Q7)
ESP_SPI_INT.PL: IC1.1 (~PL), IC2.1 (~PL), IC3.1 (~PL), IC4.1 (~PL)
ESP_SPI_INT.SCK: IC1.2 (CP), IC2.2 (CP), IC3.2 (CP), IC4.2 (CP)
GND: IC1.8 (GND), IC1.10 (DS), IC2.8 (GND), IC3.8 (GND), IC4.8 (GND)
LOCAL_A0: IC3.11 (D0)
LOCAL_A1: IC3.12 (D1)
LOCAL_A2: IC3.13 (D2)
LOCAL_A3: IC3.14 (D3)
LOCAL_A4: IC3.3 (D4)
LOCAL_A5: IC3.4 (D5)
LOCAL_A6: IC3.5 (D6)
LOCAL_A7: IC3.6 (D7)
LOCAL_A8: IC4.11 (D0)
LOCAL_A9: IC4.12 (D1)
LOCAL_A10: IC4.13 (D2)
LOCAL_A11: IC4.14 (D3)
LOCAL_A12: IC4.3 (D4)
LOCAL_A13: IC4.4 (D5)
LOCAL_A14: IC4.5 (D6)
LOCAL_A15: IC4.6 (D7)
LOCAL_D0: IC1.11 (D0)
LOCAL_D1: IC1.12 (D1)
LOCAL_D2: IC1.13 (D2)
LOCAL_D3: IC1.14 (D3)
LOCAL_D4: IC1.3 (D4)
LOCAL_D5: IC1.4 (D5)
LOCAL_D6: IC1.5 (D6)
LOCAL_D7: IC1.6 (D7)
unnamed: IC1.7 (~Q7), IC2.10 (DS)
unnamed: IC2.7 (~Q7), IC3.10 (DS)
unnamed: IC3.7 (~Q7), IC4.10 (DS)
Z80_CONTROL.BUSACK: IC2.5 (D6)
Z80_CONTROL.BUSRQ: IC2.3 (D4)
Z80_CONTROL.IORQ: IC2.13 (D2)
Z80_CONTROL.MEMRQ: IC2.14 (D3)
Z80_CONTROL.NMI: IC2.6 (D7)
Z80_CONTROL.RD: IC2.11 (D0)
Z80_CONTROL.WAIT: IC2.4 (D5)
Z80_CONTROL.WR: IC2.12 (D1)
