thweasel/FujiSim_Test1/KiCad7/FujiNet_Z80Bus_Modules/SPI-Z80-BUS_ZXspectrum/SPI-Z080-BUS_write.kicad_sch

## KiCad design KiCad7/FujiNet_Z80Bus_Modules/SPI-Z80-BUS_ZXspectrum/SPI-Z080-BUS_write.kicad_sch (2023-06-03)

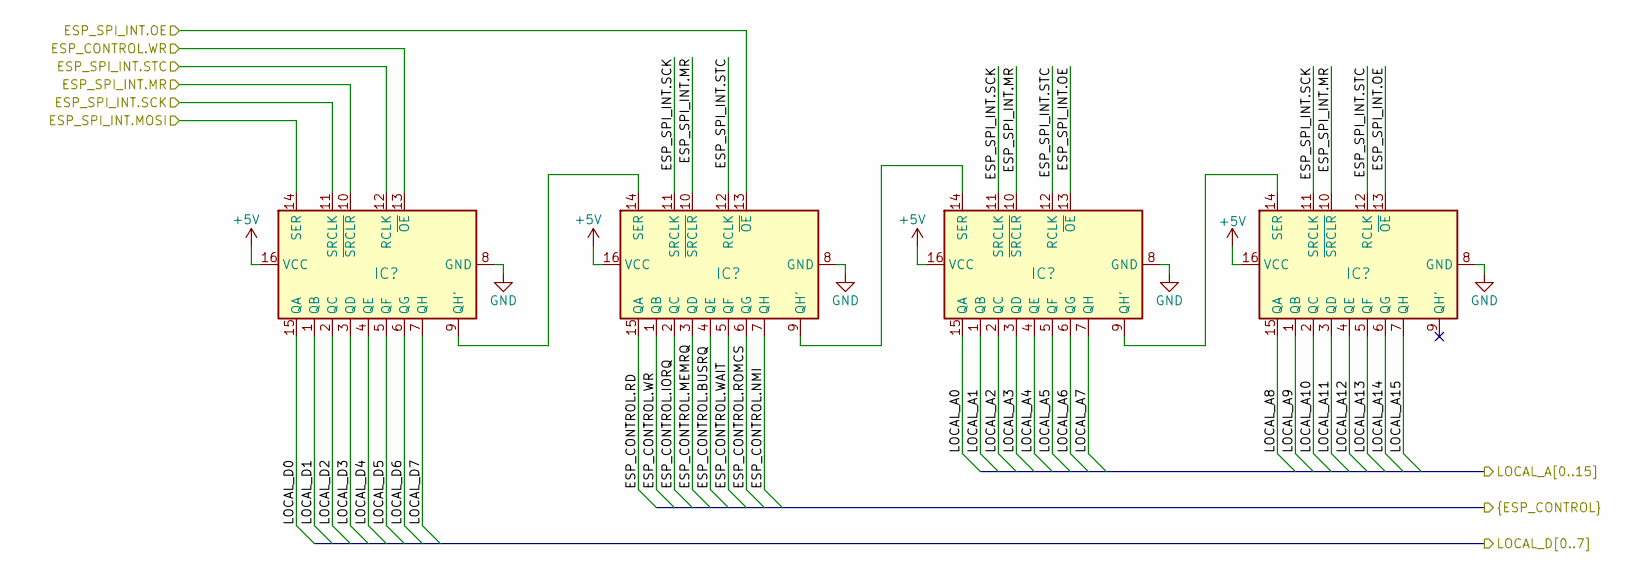
[picture p16: schematic SPI-Z080-BUS_write.kicad_sch]

Parts:
IC5, IC6, IC7, IC8: 74595N; DIP-16_W7.62mm_Socket

Connections:
+5V: IC5.16 (VCC), IC6.16 (VCC), IC7.16 (VCC), IC8.16 (VCC)
ESP_CONTROL.BUSRQ: IC6.4 (QE)
ESP_CONTROL.IORQ: IC6.2 (QC)
ESP_CONTROL.MEMRQ: IC6.3 (QD)
ESP_CONTROL.NMI: IC6.7 (QH)
ESP_CONTROL.RD: IC6.15 (QA)
ESP_CONTROL.ROMCS: IC6.6 (QG)
ESP_CONTROL.WAIT: IC6.5 (QF)
ESP_CONTROL.WR: IC5.13 (~OE), IC6.1 (QB)
ESP_SPI_INT.MOSI: IC5.14 (SER)
ESP_SPI_INT.MR: IC5.10 (~SRCLR), IC6.10 (~SRCLR), IC7.10 (~SRCLR), IC8.10 (~SRCLR)
ESP_SPI_INT.OE: IC6.13 (~OE), IC7.13 (~OE), IC8.13 (~OE)
ESP_SPI_INT.SCK: IC5.11 (SRCLK), IC6.11 (SRCLK), IC7.11 (SRCLK), IC8.11 (SRCLK)
ESP_SPI_INT.STC: IC5.12 (RCLK), IC6.12 (RCLK), IC7.12 (RCLK), IC8.12 (RCLK)
GND: IC5.8 (GND), IC6.8 (GND), IC7.8 (GND), IC8.8 (GND)
LOCAL_A0: IC7.15 (QA)
LOCAL_A1: IC7.1 (QB)
LOCAL_A2: IC7.2 (QC)
LOCAL_A3: IC7.3 (QD)
LOCAL_A4: IC7.4 (QE)
LOCAL_A5: IC7.5 (QF)
LOCAL_A6: IC7.6 (QG)
LOCAL_A7: IC7.7 (QH)
LOCAL_A8: IC8.15 (QA)
LOCAL_A9: IC8.1 (QB)
LOCAL_A10: IC8.2 (QC)
LOCAL_A11: IC8.3 (QD)
LOCAL_A12: IC8.4 (QE)
LOCAL_A13: IC8.5 (QF)
LOCAL_A14: IC8.6 (QG)
LOCAL_A15: IC8.7 (QH)
LOCAL_D0: IC5.15 (QA)
LOCAL_D1: IC5.1 (QB)
LOCAL_D2: IC5.2 (QC)
LOCAL_D3: IC5.3 (QD)
LOCAL_D4: IC5.4 (QE)
LOCAL_D5: IC5.5 (QF)
LOCAL_D6: IC5.6 (QG)
LOCAL_D7: IC5.7 (QH)
unnamed: IC5.9 (QH'), IC6.14 (SER)
unnamed: IC6.9 (QH'), IC7.14 (SER)
unnamed: IC7.9 (QH'), IC8.14 (SER)
