thweasel/FujiSim_Test1/KiCad7/FujiNet_Z80Bus_ReferenceDesign/GLUE_ZXspectrum/GLUE_ZXspectrum_connectors.kicad_sch

## KiCad design KiCad7/FujiNet_Z80Bus_ReferenceDesign/GLUE_ZXspectrum/GLUE_ZXspectrum_connectors.kicad_sch (2023-05-21)

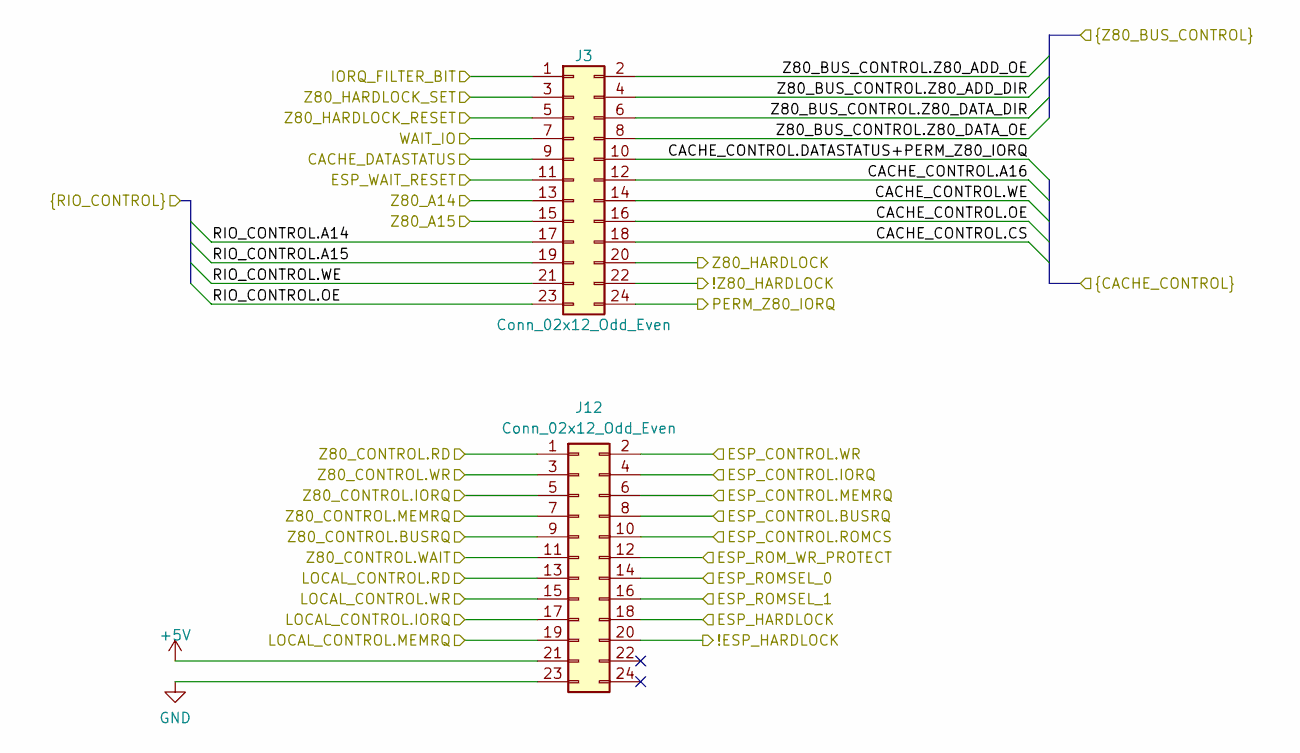
[picture p17: schematic GLUE_ZXspectrum_connectors.kicad_sch]

Parts:
J3, J12: Conn_02x12_Odd_Even; PinHeader_2x16_P2.54mm_Vertical

Connections:
!ESP_HARDLOCK: J12.20
!Z80_HARDLOCK: J3.22
+5V: J12.21
CACHE_CONTROL.A16: J3.12
CACHE_CONTROL.CS: J3.18
CACHE_CONTROL.DATASTATUS+PERM_Z80_IORQ: J3.10
CACHE_CONTROL.OE: J3.16
CACHE_CONTROL.WE: J3.14
CACHE_DATASTATUS: J3.9
ESP_CONTROL.BUSRQ: J12.8
ESP_CONTROL.IORQ: J12.4
ESP_CONTROL.MEMRQ: J12.6
ESP_CONTROL.ROMCS: J12.10
ESP_CONTROL.WR: J12.2
ESP_HARDLOCK: J12.18
ESP_ROMSEL_0: J12.14
ESP_ROMSEL_1: J12.16
ESP_ROM_WR_PROTECT: J12.12
ESP_WAIT_RESET: J3.11
GND: J12.23
IORQ_FILTER_BIT: J3.1
LOCAL_CONTROL.IORQ: J12.17
LOCAL_CONTROL.MEMRQ: J12.19
LOCAL_CONTROL.RD: J12.13
LOCAL_CONTROL.WR: J12.15
PERM_Z80_IORQ: J3.24
RIO_CONTROL.A14: J3.17
RIO_CONTROL.A15: J3.19
RIO_CONTROL.OE: J3.23
RIO_CONTROL.WE: J3.21
WAIT_IO: J3.7
Z80_A14: J3.13
Z80_A15: J3.15
Z80_BUS_CONTROL.Z80_ADD_DIR: J3.4
Z80_BUS_CONTROL.Z80_ADD_OE: J3.2
Z80_BUS_CONTROL.Z80_DATA_DIR: J3.6
Z80_BUS_CONTROL.Z80_DATA_OE: J3.8
Z80_CONTROL.BUSRQ: J12.9
Z80_CONTROL.IORQ: J12.5
Z80_CONTROL.MEMRQ: J12.7
Z80_CONTROL.RD: J12.1
Z80_CONTROL.WAIT: J12.11
Z80_CONTROL.WR: J12.3
Z80_HARDLOCK: J3.20
Z80_HARDLOCK_RESET: J3.5
Z80_HARDLOCK_SET: J3.3
