thweasel/FujiSim_Test1/KiCad7/Z80Bus_Modules/Base_Schematics/SPI-Z80-BUS_ZXspectrum_V2/SPI-Z80-BUS_ZXspectrum.kicad_sch

## KiCad design KiCad7/Z80Bus_Modules/Base_Schematics/SPI-Z80-BUS_ZXspectrum_V2/SPI-Z80-BUS_ZXspectrum.kicad_sch (2023-07-30)

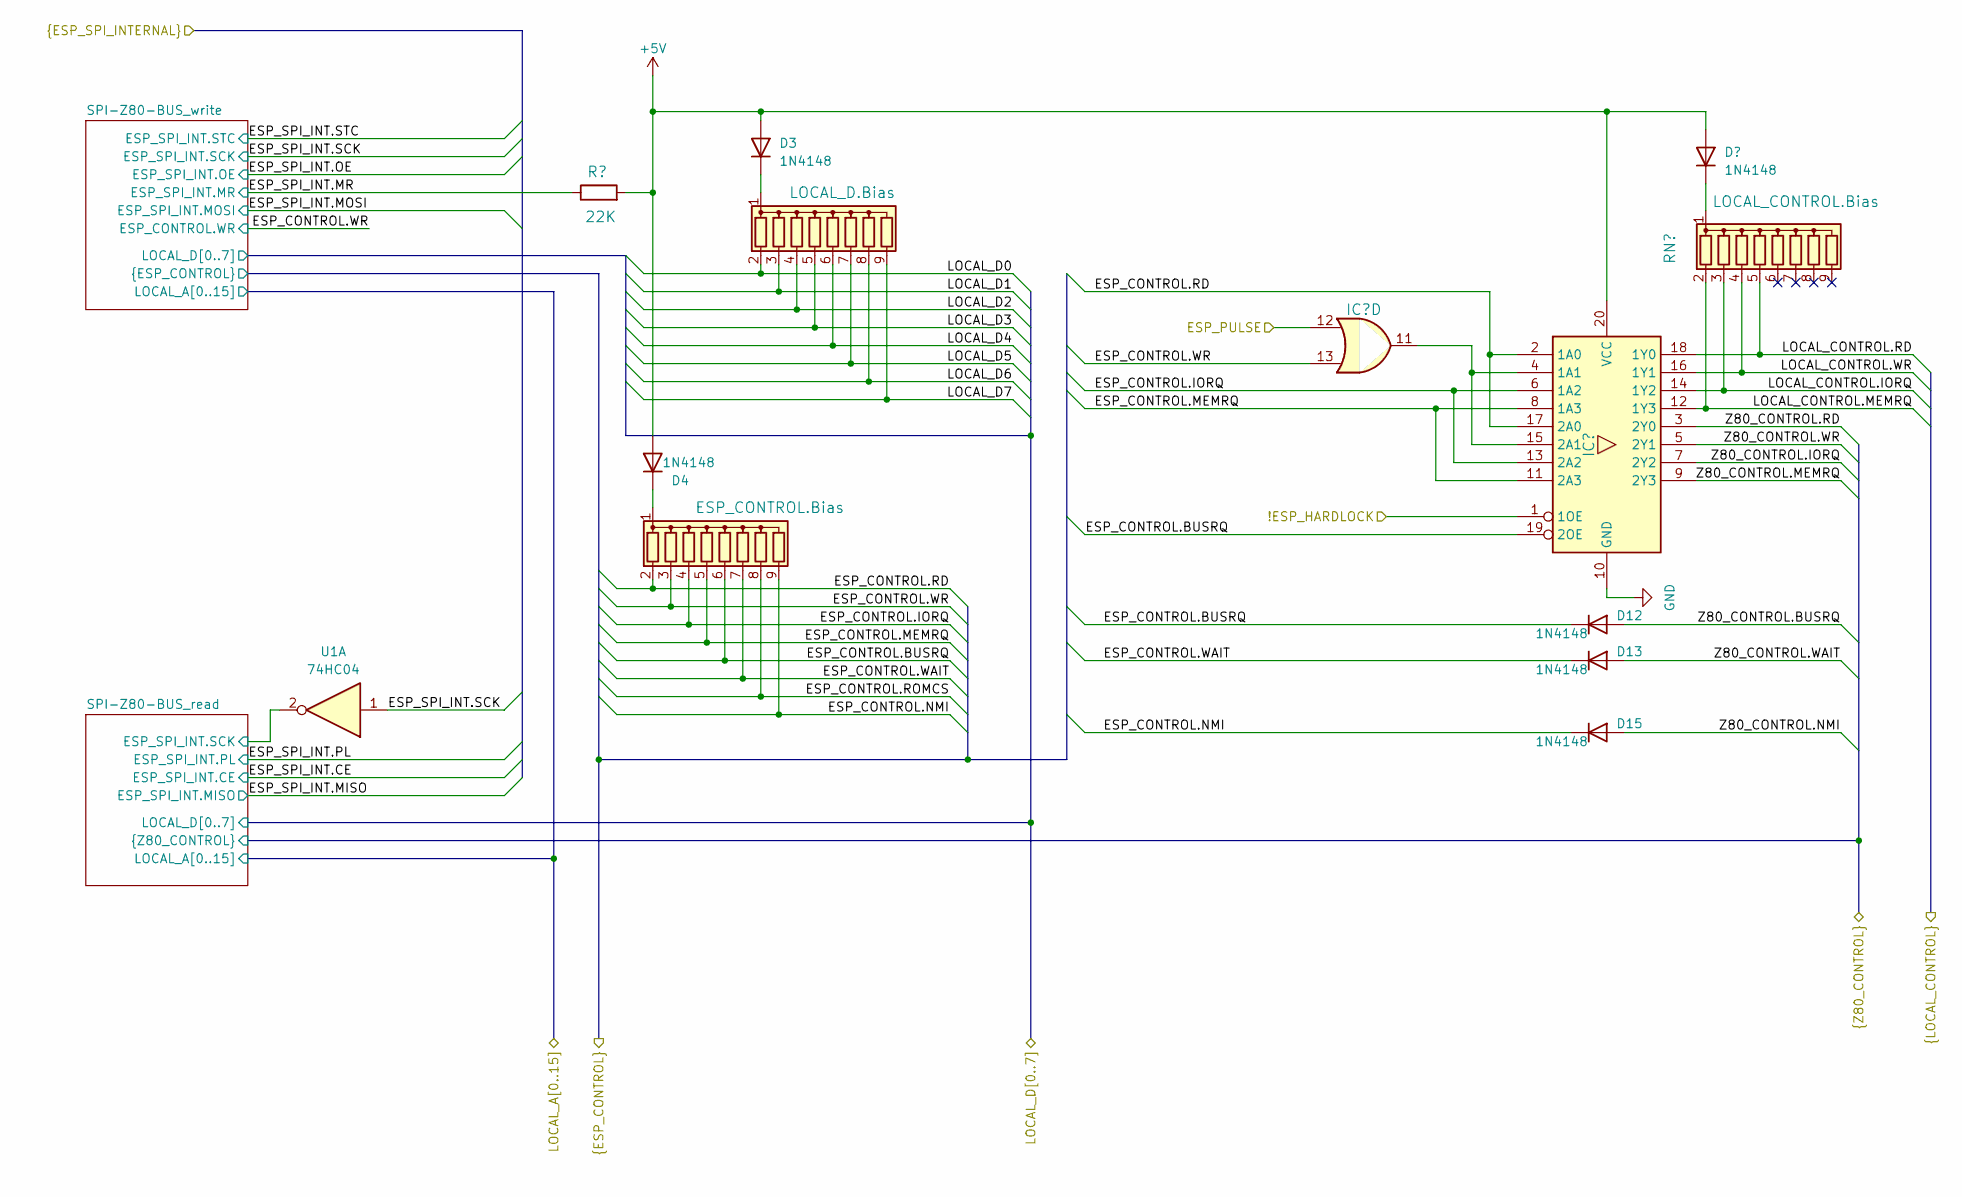
[picture p18: schematic SPI-Z80-BUS_ZXspectrum.kicad_sch]

Parts:
CONTROL.SELECT1: 74HC244N; DIP-20_W7.62mm_Socket
D3, D4, D7, D12, D13, D15: 1N4148; D_T-1_P5.08mm_Horizontal
ESP_CONTROL.Bias: 4609M-101-103LF; R_Array_SIP9
IC1: 74HC32N; DIP-14_W7.62mm_Socket
LOCAL_D.Bias: 4609M-101-103LF; R_Array_SIP9
R1: 22K; R_Axial_DIN0207_L6.3mm_D2.5mm_P10.16mm_Horizontal
RN1: LOCAL_CONTROL.Bias; R_Array_SIP9
U1: 74HC04

Connections:
!ESP_HARDLOCK: CONTROL.SELECT1.1 (1OE)
+5V: CONTROL.SELECT1.20 (VCC), D3.2 (A), D4.2 (A), D7.2 (A), R1.2
ESP_CONTROL.BUSRQ: CONTROL.SELECT1.19 (2OE), D12.1 (K), ESP_CONTROL.Bias.6 (R5)
ESP_CONTROL.IORQ: CONTROL.SELECT1.6 (1A2), CONTROL.SELECT1.13 (2A2), ESP_CONTROL.Bias.4 (R3)
ESP_CONTROL.MEMRQ: CONTROL.SELECT1.8 (1A3), CONTROL.SELECT1.11 (2A3), ESP_CONTROL.Bias.5 (R4)
ESP_CONTROL.NMI: D15.1 (K), ESP_CONTROL.Bias.9 (R8)
ESP_CONTROL.RD: CONTROL.SELECT1.2 (1A0), CONTROL.SELECT1.17 (2A0), ESP_CONTROL.Bias.2 (R1)
ESP_CONTROL.ROMCS: ESP_CONTROL.Bias.8 (R7)
ESP_CONTROL.WAIT: D13.1 (K), ESP_CONTROL.Bias.7 (R6)
ESP_CONTROL.WR: ESP_CONTROL.Bias.3 (R2), IC1.13
ESP_PULSE: IC1.12
ESP_SPI_INT.MR: R1.1
ESP_SPI_INT.SCK: U1.1, U1.2
GND: CONTROL.SELECT1.10 (GND)
LOCAL_CONTROL.IORQ: CONTROL.SELECT1.14 (1Y2), RN1.3 (R2)
LOCAL_CONTROL.MEMRQ: CONTROL.SELECT1.12 (1Y3), RN1.2 (R1)
LOCAL_CONTROL.RD: CONTROL.SELECT1.18 (1Y0), RN1.5 (R4)
LOCAL_CONTROL.WR: CONTROL.SELECT1.16 (1Y1), RN1.4 (R3)
LOCAL_D0: LOCAL_D.Bias.2 (R1)
LOCAL_D1: LOCAL_D.Bias.3 (R2)
LOCAL_D2: LOCAL_D.Bias.4 (R3)
LOCAL_D3: LOCAL_D.Bias.5 (R4)
LOCAL_D4: LOCAL_D.Bias.6 (R5)
LOCAL_D5: LOCAL_D.Bias.7 (R6)
LOCAL_D6: LOCAL_D.Bias.8 (R7)
LOCAL_D7: LOCAL_D.Bias.9 (R8)
unnamed: CONTROL.SELECT1.4 (1A1), CONTROL.SELECT1.15 (2A1), IC1.11
unnamed: D3.1 (K), LOCAL_D.Bias.1 (common)
unnamed: D4.1 (K), ESP_CONTROL.Bias.1 (common)
unnamed: D7.1 (K), RN1.1 (common)
Z80_CONTROL.BUSRQ: D12.2 (A)
Z80_CONTROL.IORQ: CONTROL.SELECT1.7 (2Y2)
Z80_CONTROL.MEMRQ: CONTROL.SELECT1.9 (2Y3)
Z80_CONTROL.NMI: D15.2 (A)
Z80_CONTROL.RD: CONTROL.SELECT1.3 (2Y0)
Z80_CONTROL.WAIT: D13.2 (A)
Z80_CONTROL.WR: CONTROL.SELECT1.5 (2Y1)
