thweasel/FujiSim_Test1/src/ESPSystemInterface.cpp

#include "ESPemulation.h"

uint8_t *BUSbytesPTR;
//  BUSbyte [3] = Data;
//  BUSbyte [2] = Control;
//  BUSbyte [1] = loAddr;
//  BUSbyte [0] = hiAddr;


void ESPsetup(void)
{
  // ESP pin Config
  pinMode(ESPout_STC, OUTPUT);
  pinMode(ESPout_OE, OUTPUT);
  pinMode(ESP_PULSE, OUTPUT);
  pinMode(ESPin_PL, OUTPUT);
  pinMode(ESP_ROMSELECT0, OUTPUT);
  pinMode(ESP_ROMSELECT1, OUTPUT);
  pinMode(ESP_espHARDLOCK, OUTPUT);
  pinMode(ESP_z80HARDLOCK, INPUT);
  pinMode(CONNECT_Z80, OUTPUT);

  // ESP pin State
  digitalWrite(ESPout_STC, HIGH);
  digitalWrite(ESPout_OE, HIGH);
  digitalWrite(ESP_PULSE, HIGH);
  digitalWrite(ESPin_PL, HIGH);
  digitalWrite(ESP_ROMSELECT0, LOW);
  digitalWrite(ESP_ROMSELECT1, LOW);
  digitalWrite(ESP_espHARDLOCK, HIGH); // Lock set LOW
  digitalWrite(ESP_z80HARDLOCK, HIGH); // Lock set LOW
  digitalWrite(CONNECT_Z80, HIGH);  // Connect on LOW (may be buffer with NOT?)


  // ESP Warm up -- FUJI setup will be needed here at somepoint
  clearBUS();
  resetESPHardlock();
  // Program the IOd & ROMs
}



//
//  Z80 BUS Interactions
//

// Everything in here should be done under a BUSRQ which disables the Z80

// ESP accessing the ROM/IOd chip VIA Z80 Bus
// Uses these to read/write ROMs into the IOd chip
uint8_t doCEROMRead(uint16_t Address, uint8_t ROMbank) // A16-0
{
    doBUSRQ();
    selectROMbank(ROMbank);
    // Z80 CE
    //connectZ80Bus();

    BUSbytesPTR = doBUSRead(Address, CONTROLBYTE_CEROMRQ_RD);

    clearBUS();

    return BUSbytesPTR[3];
}

void doCEROMWrite(uint8_t Data, uint16_t Address, uint8_t ROMbank) // A16-0
{
    doBUSRQ();
    selectROMbank(ROMbank);
    //connectZ80Bus();

    doBUSWrite(Data, Address, CONTROLBYTE_CEROMRQ_WR);

    clearBUS();
}

// These methods are for programming the IOd configuration bytes
uint8_t doIOdRead(uint16_t Address) // A16-1
{
    doBUSRQ();
    setESPHardlock();

    // connect Z80Data and ROM/IOdbus

    BUSbytesPTR = doBUSRead(Address, CONTROLBYTE_IORQ_RD);

    clearBUS();
    resetESPHardlock();
    return BUSbytesPTR[3];
}

void doIOdWrite(uint8_t Data, uint16_t Address) // A16-1
{
    doBUSRQ();
    setESPHardlock();
    // connect Z80Data and ROM/IOdbus

    doBUSWrite(Data, Address, CONTROLBYTE_IORQ_WR);

    clearBUS();
    resetESPHardlock();
}

// ESP controlling the system in place of the Z80
// Direct access to the host system memory
uint8_t doZ80MEMRead(uint16_t Address)
{
    doBUSRQ();

    BUSbytesPTR = doBUSRead(Address, CONTROLBYTE_MEMRQ_RD);

    clearBUS();
    return BUSbytesPTR[3];
}

void doZ80MEMWrite(uint8_t Data, uint16_t Address)
{
    doBUSRQ();

    doBUSWrite(Data, Address, CONTROLBYTE_MEMRQ_WR);

    clearBUS();
}

// IO calls may be needed to access system memory bank registers etc
// Probably will not be much use for interacting with actual hardware (does not create true bus timings)
uint8_t doZ80IORead(uint16_t Address)
{
    doBUSRQ();

    BUSbytesPTR = doBUSRead(Address, CONTROLBYTE_IORQ_RD);

    clearBUS();
    return BUSbytesPTR[3];
}

void doZ80IOWrite(uint8_t Data, uint16_t Address)
{
    doBUSRQ();

    doBUSWrite(Data, Address, CONTROLBYTE_IORQ_WR);

    clearBUS();
}


//
//  LOCAL BUS Interactions
//

// All actions here should be done under ESP-HARDLOCK conditions
// The Z80 (Host) will not be able to lock or use the system while ESP is accessing it

// ESP accessing Cache chip
uint8_t doCacheDataRead(uint16_t Address) // A16-0
{
    setESPHardlock();

    BUSbytesPTR = doBUSRead(Address, CONTROLBYTE_CACHEDATA_RD);

    clearBUS();
    resetESPHardlock();
    return BUSbytesPTR[3];
}

void doCacheDataWrite(uint8_t Data, uint16_t Address) // A16-0
{
    setESPHardlock();

    doBUSWrite(Data, Address, CONTROLBYTE_CACHEDATA_WR);

    clearBUS();
    resetESPHardlock();
}

uint8_t doCacheStatusRead(uint16_t Address) // A16-1
{
    setESPHardlock();

    BUSbytesPTR = doBUSRead(Address, CONTROLBYTE_CACHESTATUS_RD);

    digitalWrite(ESP_ROMSELECT0, HIGH);

    clearBUS();
    resetESPHardlock();
    return BUSbytesPTR[3];
}

void doCacheStatusWrite(uint8_t Data, uint16_t Address) // A16-1
{
    setESPHardlock();

    doBUSWrite(Data, Address, CONTROLBYTE_CACHESTATUS_WR);
    
    clearBUS();
    resetESPHardlock();
}
