thweasel/FujiSim_Test1/src/ESPemulation.cpp

#include <ESPemulation.h>

SPISettings mySpiSettings_write (40000,MSBFIRST,SPI_MODE0);
SPISettings mySpiSettings_read (40000,MSBFIRST,SPI_MODE0);

//SPISettings mySpiSettings_write (500000,MSBFIRST,SPI_MODE1);
//SPISettings mySpiSettings_read (500000,MSBFIRST,SPI_MODE3);

uint8_t SPIpacketTX[4]; 
uint8_t SPIpacketRX[4];

// SPI PACKET BYTES
//  SPIpacketTX[3] = Data;
//  SPIpacketTX[2] = Control;
//  SPIpacketTX[1] = loAddr;
//  SPIpacketTX[0] = hiAddr;

//void transfer(void *buf, size_t count)

void clearSPIpacketRX (void)
{
  SPIpacketTX[3] = 0xFF;
  SPIpacketTX[2] = 0xFF;
  SPIpacketTX[1] = 0xFF;
  SPIpacketTX[0] = 0xFF;
}


// ESP SPI Bus and Pin controls
uint8_t * setSPIpacketTX (uint8_t Data, uint8_t Control, uint16_t Address)
{

  uint8_t loAddr = (uint8_t)(Address);
  uint8_t hiAddr = (uint8_t)(Address >> 8);

  SPIpacketTX[3] = Data;
  SPIpacketTX[2] = Control;
  SPIpacketTX[1] = loAddr;
  SPIpacketTX[0] = hiAddr;

  return SPIpacketTX;
}

// ROM Select
void selectROMbank(uint8_t rom)
{
  if (rom < 4)
  {
    // set rom selection pins
  }
  else
  {
    // error condition here
  }

  return;
}

// Some actions need a clock pulse to trigger, use this.
void sendPULSE(void)
{
  digitalWrite(ESP_PULSE,ENABLE_LOW);
  digitalWrite(ESP_PULSE,DISABLE_HIGH);
  return;
}

bool setESPHardlock(void)
{  // This should check for the Z80 lock, then block or return false
  digitalWrite(ESP_espHARDLOCK,ENABLE_LOW);
  while(1 == digitalRead(ESP_z80HARDLOCK))
  {
    delay(1); // wait -- block
  }
  
  return true;
}

bool resetESPHardlock(void)
{
  digitalWrite(ESP_espHARDLOCK,DISABLE_HIGH);
  return true;
}




// SPI Write ESPout
void writeSPI(void)
{ 
  // OUTPUT 74XX595 Shift registers (x4)
  
  // Load TXPacket into the Shift Regs
  SPI.beginTransaction(mySpiSettings_write);
  SPI.transfer(SPIpacketTX,4);  
  SPI.endTransaction();

  // LATCH the Shift Regs to Storage (pulse)
  digitalWrite(ESPout_STC, HIGH); // Move shift to storage
  digitalWrite(ESPout_STC, LOW);
  
  // Enable the Output from the 595s
  digitalWrite(ESPout_OE, ENABLE_LOW);

  delay(10);

  return;
}

// SPI Read the ESPin
void readSPI(void)
{ 
  // INPUT 74xx165 Shift Registers (x4)

  // LATCH data into the Shift Regs (pulse)
  digitalWrite(ESPin_PL, LOW);  // Parallel Load
  
  // Unload the Shift Reg to RXPacket
  digitalWrite(ESPin_PL, HIGH); // Serial Shift
  
  SPI.beginTransaction(mySpiSettings_read);
  SPI.transfer(SPIpacketRX,4);  
  SPI.endTransaction();

  delay(10);

  digitalWrite(ESPout_OE,DISABLE_HIGH);  // Remove Control & Address  
  
}

// ESP Parallel BUS Functions

void clearBUS()
{  
  digitalWrite(ESPout_OE,HIGH);  // disconnect S-Regs from BUS
}


bool doBUSRQ(void)
{
  setSPIpacketTX(0xFF,CONTROLBYTE_BUSRQ,0xFFFF);
  writeSPI();
  // WAIT HERE FOR THE BUSACK signal
  delay(10);
  
  return true;
}

bool resetBUSRQ(void)
{
  // Clear BUS will do it.
  return true;
}

uint8_t * doBUSRead(uint16_t Address, uint8_t Control)
{
  setSPIpacketTX(0x0, Control, Address);
  writeSPI(); // Set Control and Address lines
  
  //clearSPIpacketRX();
  readSPI();
  //clearBUS();
  return SPIpacketRX;
}

void doBUSWrite(uint8_t Data, uint16_t Address, uint8_t Control)
{
  setSPIpacketTX(Data, Control, Address);
  writeSPI();
  sendPULSE();
  //clearBUS();
  return;
}
